unirsm/openMuseum/reader/img/kit.jpg

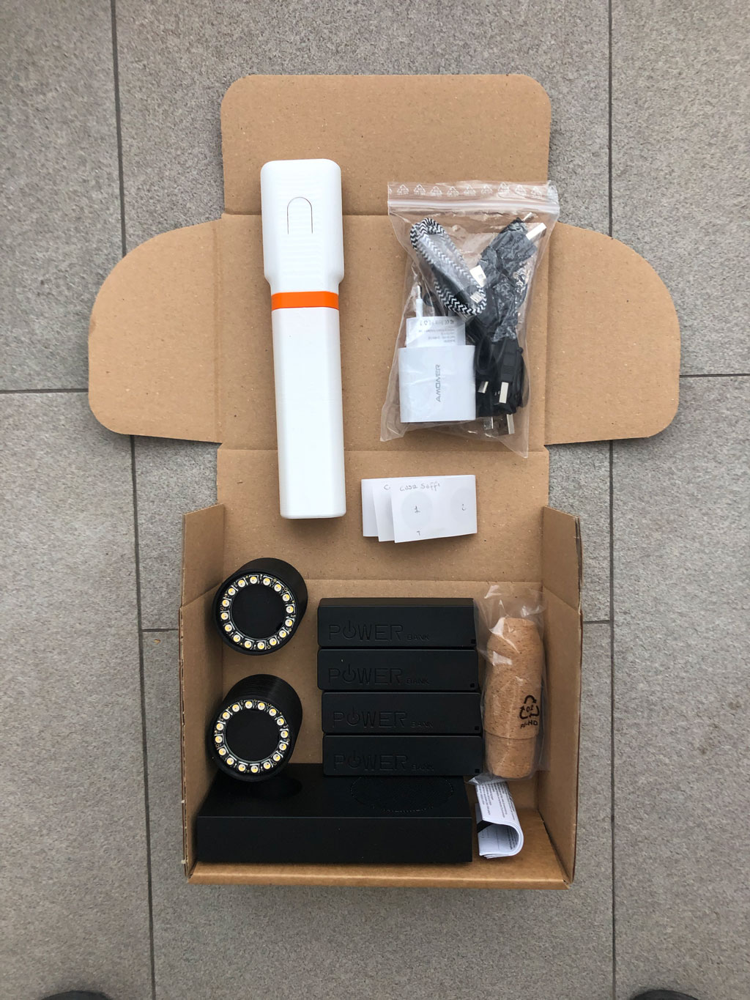
reader/img/kit.jpg
